ArcaEge/capacitor-alarm-clock/pcb/EASYEDA_MODELS/SOT-223-4P_L6.5-W3.5-H1.6-LS7.0-P2.30.step

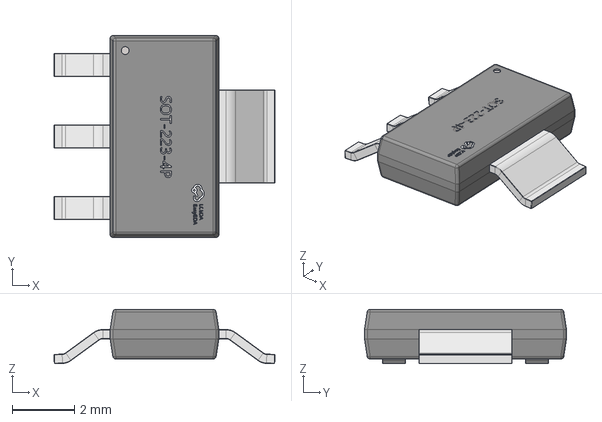
[picture p26: CAD file, 2026-04-05]
pcb/EASYEDA_MODELS/SOT-223-4P_L6.5-W3.5-H1.6-LS7.0-P2.30.step
7.11 x 6.50 x 1.75 mm
