ArcaEge/capacitor-alarm-clock/pcb/EASYEDA_MODELS/SW-SMD_4P-L4.2-W3.3-H2.5-P2.15-LS5.1.step

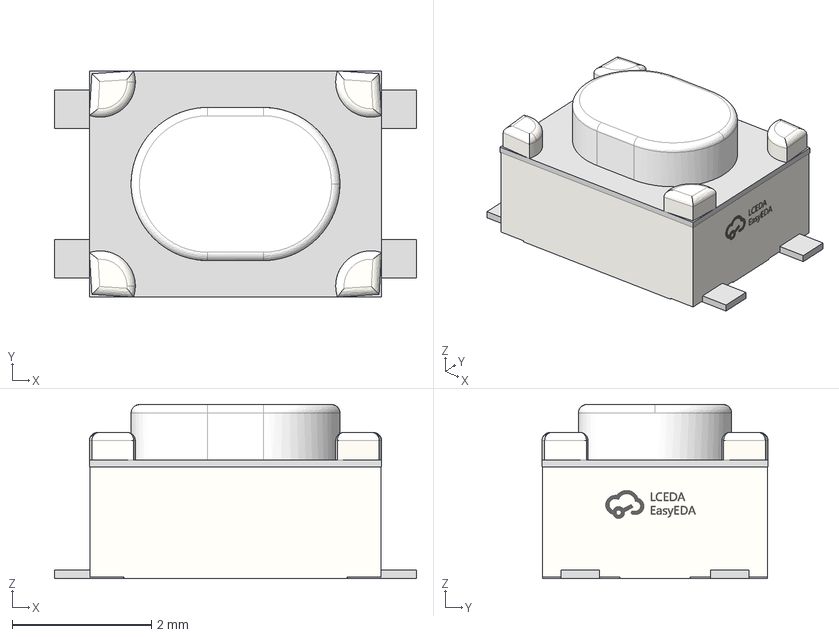
[picture p27: CAD file, 2026-04-05]
pcb/EASYEDA_MODELS/SW-SMD_4P-L4.2-W3.3-H2.5-P2.15-LS5.1.step
5.20 x 3.25 x 2.50 mm
