ArcaEge/capacitor-alarm-clock/pcb/EASYEDA_MODELS/HDR2.54-M-LI-1X2P.step

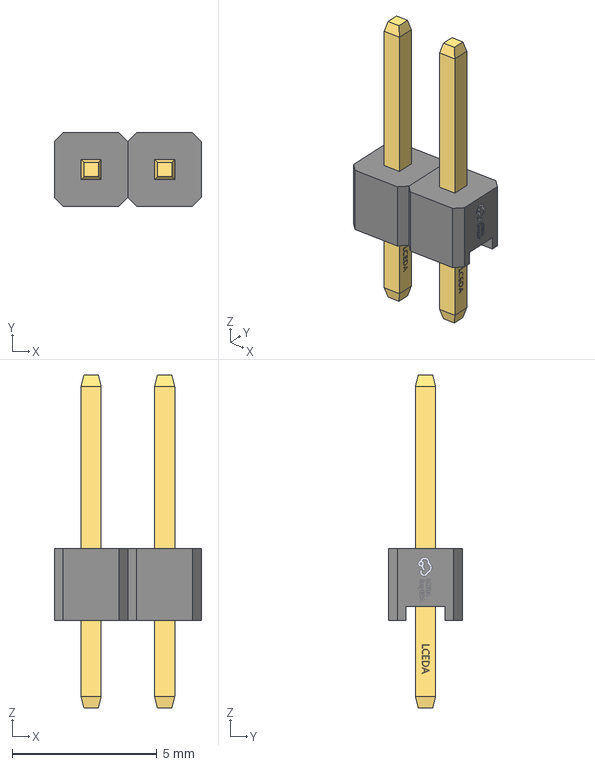
[picture p28: CAD file, 2026-04-05]
pcb/EASYEDA_MODELS/HDR2.54-M-LI-1X2P.step
5.09 x 2.54 x 11.5 mm
