ArcaEge/capacitor-alarm-clock/pcb/EASYEDA_MODELS/HDR-TH_4P-P2.54-M-LI-1X4P.step

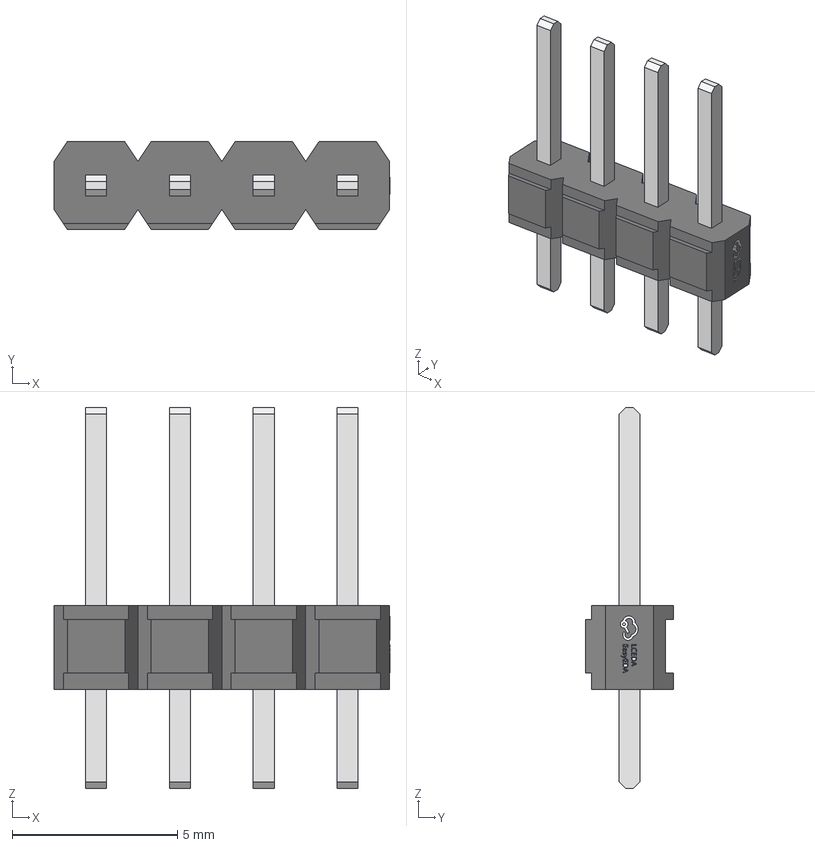
[picture p29: CAD file, 2026-04-05]
pcb/EASYEDA_MODELS/HDR-TH_4P-P2.54-M-LI-1X4P.step
10.2 x 2.66 x 11.5 mm
