ArcaEge/capacitor-alarm-clock/pcb/EASYEDA_MODELS/PWRM-TH_WRAXXXXSD-3WR2.step

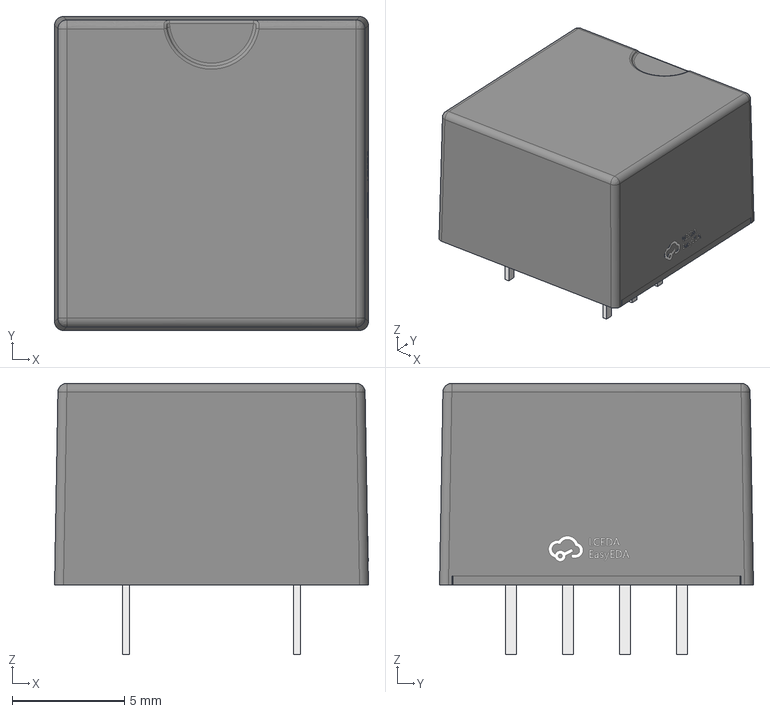
[picture p30: CAD file, 2026-04-04]
pcb/EASYEDA_MODELS/PWRM-TH_WRAXXXXSD-3WR2.step
14.0 x 14.0 x 12.1 mm
