ArcaEge/capacitor-alarm-clock/pcb/EASYEDA_MODELS/OSC-SMD_4P-L2.5-W2.0-H0.6.step

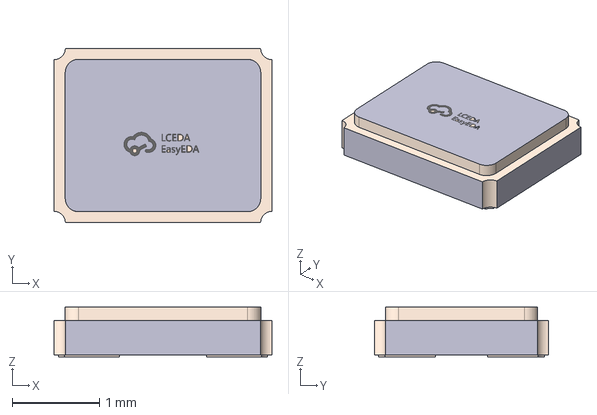
[picture p31: CAD file, 2026-04-04]
pcb/EASYEDA_MODELS/OSC-SMD_4P-L2.5-W2.0-H0.6.step
2.50 x 2.00 x 0.571 mm
