ArcaEge/capacitor-alarm-clock/pcb/EASYEDA_MODELS/USB-C-SMD_TYPE-C-6PIN-2MD-073.step

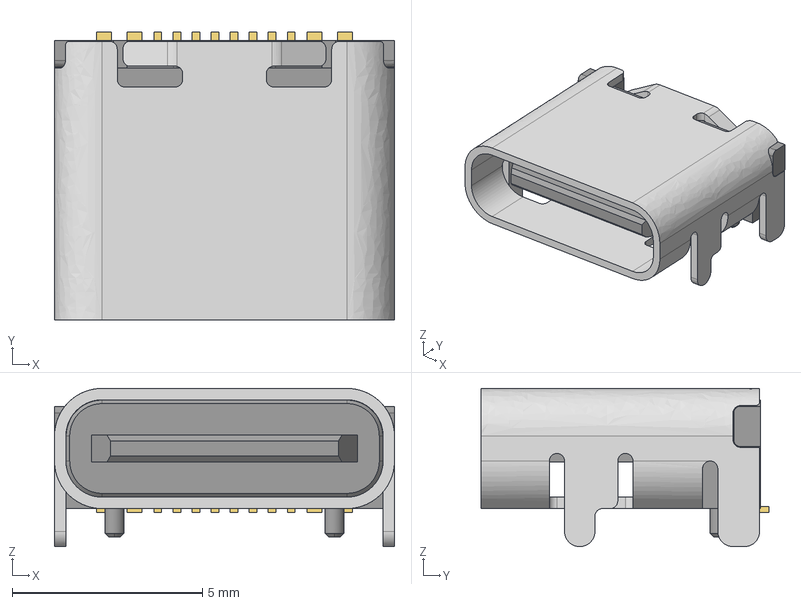
[picture p32: CAD file, 2026-04-04]
pcb/EASYEDA_MODELS/USB-C-SMD_TYPE-C-6PIN-2MD-073.step
8.94 x 7.58 x 4.16 mm
