ArcaEge/capacitor-alarm-clock/pcb/EASYEDA_MODELS/WIFIM-SMD_ESP32-C3-MINI-1.step

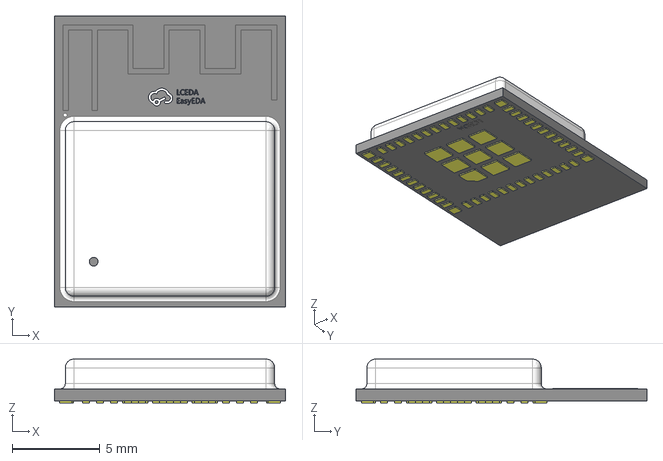
[picture p33: CAD file, 2026-04-04]
pcb/EASYEDA_MODELS/WIFIM-SMD_ESP32-C3-MINI-1.step
13.2 x 16.6 x 2.50 mm
